siliconvalleyar-oss/pico_hw_kcd/docs/3.gif

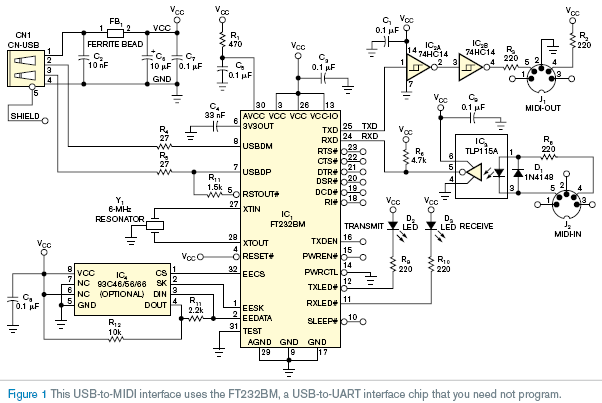
docs/3.gif
