siliconvalleyar-oss/pico_hw_kcd/docs/canvas.png

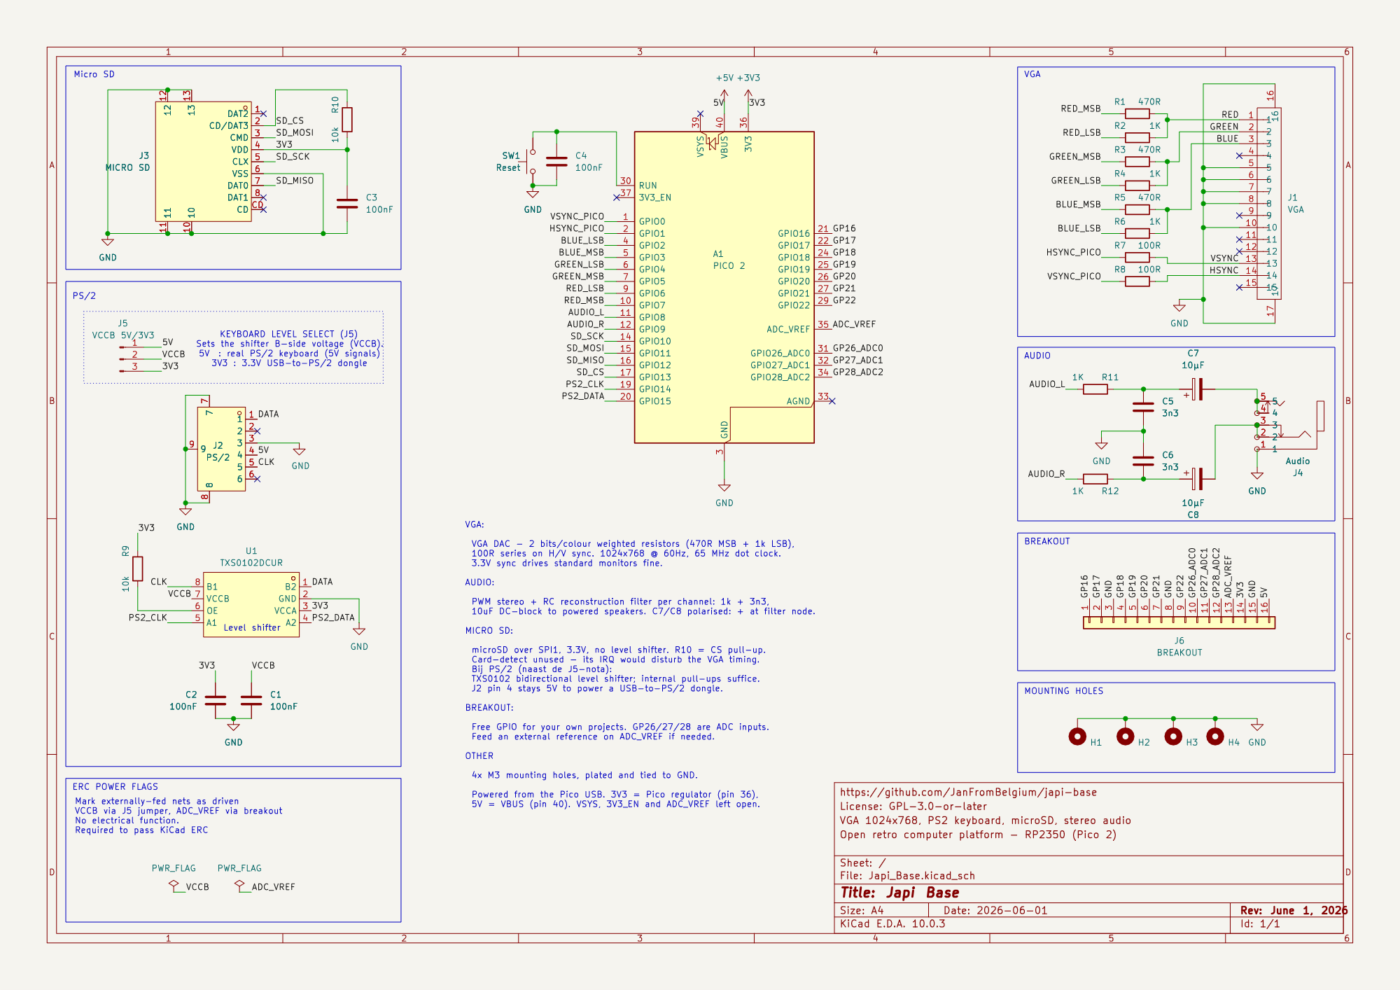
docs/canvas.png
