siliconvalleyar-oss/pico_hw_kcd/docs/ft232BM.png

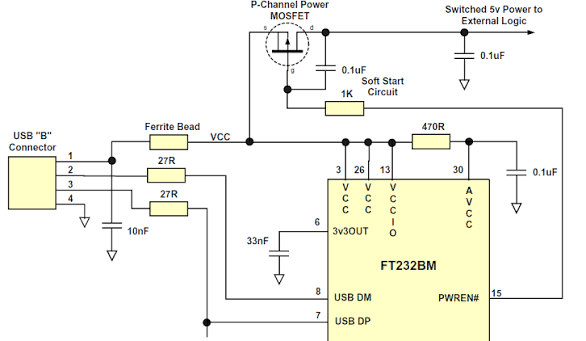
docs/ft232BM.png
